Wireb/ICE40LP384_RPi_breakout/iCEcube2/PiDRO_Implmnt/sbt/outputs/placer/PiDRO_sbt.pcf

set_location SPI.SDO_RNO 5 3 6 # SB_LUT4 (LogicCell: SPI.SDO_LC_0)
set_location SPI.SDO 5 3 6 # SB_DFFNE (LogicCell: SPI.SDO_LC_0)
set_location SPI.SDO_RNO_0 5 4 7 # SB_LUT4 (LogicCell: SPI.SDO_RNO_0_LC_1)
set_location SPI.shift_reg_RNO[1] 2 2 5 # SB_LUT4 (LogicCell: SPI.shift_reg[1]_LC_2)
set_location SPI.shift_reg[1] 2 2 5 # SB_DFFN (LogicCell: SPI.shift_reg[1]_LC_2)
set_location SPI.shift_reg_RNO[10] 2 3 0 # SB_LUT4 (LogicCell: SPI.shift_reg[10]_LC_3)
set_location SPI.shift_reg[10] 2 3 0 # SB_DFFN (LogicCell: SPI.shift_reg[10]_LC_3)
set_location SPI.shift_reg_RNO[100] 4 1 1 # SB_LUT4 (LogicCell: SPI.shift_reg[100]_LC_4)
set_location SPI.shift_reg[100] 4 1 1 # SB_DFFN (LogicCell: SPI.shift_reg[100]_LC_4)
set_location SPI.shift_reg_RNO[101] 4 1 6 # SB_LUT4 (LogicCell: SPI.shift_reg[101]_LC_5)
set_location SPI.shift_reg[101] 4 1 6 # SB_DFFN (LogicCell: SPI.shift_reg[101]_LC_5)
set_location SPI.shift_reg_RNO[102] 4 1 3 # SB_LUT4 (LogicCell: SPI.shift_reg[102]_LC_6)
set_location SPI.shift_reg[102] 4 1 3 # SB_DFFN (LogicCell: SPI.shift_reg[102]_LC_6)
set_location SPI.shift_reg_RNO[103] 4 1 4 # SB_LUT4 (LogicCell: SPI.shift_reg[103]_LC_7)
set_location SPI.shift_reg[103] 4 1 4 # SB_DFFN (LogicCell: SPI.shift_reg[103]_LC_7)
set_location SPI.shift_reg_RNO[104] 4 1 2 # SB_LUT4 (LogicCell: SPI.shift_reg[104]_LC_8)
set_location SPI.shift_reg[104] 4 1 2 # SB_DFFN (LogicCell: SPI.shift_reg[104]_LC_8)
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
set_location SPI.shift_reg[97] 5 1 3 # SB_DFFN (LogicCell: SPI.shift_reg[97]_LC_118)
set_location SPI.shift_reg_RNO[98] 5 1 2 # SB_LUT4 (LogicCell: SPI.shift_reg[98]_LC_119)
set_location SPI.shift_reg[98] 5 1 2 # SB_DFFN (LogicCell: SPI.shift_reg[98]_LC_119)
set_location SPI.shift_reg_RNO[99] 5 1 0 # SB_LUT4 (LogicCell: SPI.shift_reg[99]_LC_120)
set_location SPI.shift_reg[99] 5 1 0 # SB_DFFN (LogicCell: SPI.shift_reg[99]_LC_120)
set_location SPI.shift_reg_0_THRU_LUT4_0 2 1 7 # SB_LUT4 (LogicCell: SPI.shift_reg[0]_LC_121)
set_location SPI.shift_reg[0] 2 1 7 # SB_DFFN (LogicCell: SPI.shift_reg[0]_LC_121)
set_location SPI.shift_reg_rst_THRU_LUT4_0 3 3 0 # SB_LUT4 (LogicCell: SPI.shift_reg_rst_LC_122)
set_location SPI.shift_reg_rst 3 3 0 # SB_DFFNR (LogicCell: SPI.shift_reg_rst_LC_122)
set_location SPI.shift_reg_rst_fast_THRU_LUT4_0 5 2 6 # SB_LUT4 (LogicCell: SPI.shift_reg_rst_fast_LC_123)
set_location SPI.shift_reg_rst_fast 5 2 6 # SB_DFFNR (LogicCell: SPI.shift_reg_rst_fast_LC_123)
set_location SPI.shift_reg_rst_fast_0_THRU_LUT4_0 3 3 2 # SB_LUT4 (LogicCell: SPI.shift_reg_rst_fast_0_LC_124)
set_location SPI.shift_reg_rst_fast_0 3 3 2 # SB_DFFNR (LogicCell: SPI.shift_reg_rst_fast_0_LC_124)
set_location SPI.shift_reg_rst_fast_fast_THRU_LUT4_0 3 3 3 # SB_LUT4 (LogicCell: SPI.shift_reg_rst_fast_fast_LC_125)
set_location SPI.shift_reg_rst_fast_fast 3 3 3 # SB_DFFNR (LogicCell: SPI.shift_reg_rst_fast_fast_LC_125)
set_location SPI.shift_reg_rst_fast_rep1_THRU_LUT4_0 3 1 4 # SB_LUT4 (LogicCell: SPI.shift_reg_rst_fast_rep1_LC_126)
set_location SPI.shift_reg_rst_fast_rep1 3 1 4 # SB_DFFNR (LogicCell: SPI.shift_reg_rst_fast_rep1_LC_126)
set_location SPI.shift_reg_rst_rep1_THRU_LUT4_0 3 3 5 # SB_LUT4 (LogicCell: SPI.shift_reg_rst_rep1_LC_127)
set_location SPI.shift_reg_rst_rep1 3 3 5 # SB_DFFNR (LogicCell: SPI.shift_reg_rst_rep1_LC_127)
set_location SPI.shift_reg_rst_rep1_0_THRU_LUT4_0 3 3 6 # SB_LUT4 (LogicCell: SPI.shift_reg_rst_rep1_0_LC_128)
set_location SPI.shift_reg_rst_rep1_0 3 3 6 # SB_DFFNR (LogicCell: SPI.shift_reg_rst_rep1_0_LC_128)
set_location SPI.shift_reg_rst_rep1_fast_THRU_LUT4_0 3 3 7 # SB_LUT4 (LogicCell: SPI.shift_reg_rst_rep1_fast_LC_129)
set_location SPI.shift_reg_rst_rep1_fast 3 3 7 # SB_DFFNR (LogicCell: SPI.shift_reg_rst_rep1_fast_LC_129)
set_location SPI.shift_reg_rst_rep1_rep1_THRU_LUT4_0 4 6 0 # SB_LUT4 (LogicCell: SPI.shift_reg_rst_rep1_rep1_LC_130)
set_location SPI.shift_reg_rst_rep1_rep1 4 6 0 # SB_DFFNR (LogicCell: SPI.shift_reg_rst_rep1_rep1_LC_130)
set_location SPI.shift_reg_rst_rep2_THRU_LUT4_0 4 6 1 # SB_LUT4 (LogicCell: SPI.shift_reg_rst_rep2_LC_131)
set_location SPI.shift_reg_rst_rep2 4 6 1 # SB_DFFNR (LogicCell: SPI.shift_reg_rst_rep2_LC_131)
set_location SPI.shift_reg_rst_rep2_fast_THRU_LUT4_0 4 6 2 # SB_LUT4 (LogicCell: SPI.shift_reg_rst_rep2_fast_LC_132)
set_location SPI.shift_reg_rst_rep2_fast 4 6 2 # SB_DFFNR (LogicCell: SPI.shift_reg_rst_rep2_fast_LC_132)
set_location SPI.shift_reg_rst_rep2_rep1_THRU_LUT4_0 4 6 3 # SB_LUT4 (LogicCell: SPI.shift_reg_rst_rep2_rep1_LC_133)
set_location SPI.shift_reg_rst_rep2_rep1 4 6 3 # SB_DFFNR (LogicCell: SPI.shift_reg_rst_rep2_rep1_LC_133)
set_location GND -1 -1 -1 # GND
set_io LED_obuf 7 4 0 # ICE_IO
set_io SPI_SDI_ibuf 5 0 1 # ICE_IO
set_io SPI_SDO_obuf 5 0 0 # ICE_IO
set_io SPI_SS_ibuf 6 0 1 # ICE_IO
set_io SPI_SCK_ibuf_gb_io 6 0 0 # ICE_IO
set_io SPI_SCK_ibuf_gb_io_gb 0 5 0 # ICE_GB
set_location INV_SPI_SCK_c_g -1 -1 -1 # INV
set_location CONSTANT_ONE_LUT4 5 6 7 # SB_LUT4 (LogicCell: LC_134)
