Wireb/ICE40LP384_RPi_breakout/iCEcube2/PiDRO_Implmnt/sbt/outputs/simulation_netlist/main_sbt.vhd

-- ******************************************************************************

-- iCEcube Netlister

-- Version:            2020.12.27943

-- Build Date:         Dec  9 2020 18:18:06

-- File Generated:     Mar 20 2022 17:01:08

-- Purpose:            Post-Route Verilog/VHDL netlist for timing simulation

-- Copyright (C) 2006-2010 by Lattice Semiconductor Corp. All rights reserved.

-- ******************************************************************************

-- VHDL file for cell "main" view "INTERFACE"

library ieee;
use ieee.std_logic_1164.all;
use ieee.std_logic_arith.all;
use ieee.std_logic_unsigned.all;

library ice;
use ice.vcomponent_vital.all;

-- Entity of main
entity main is
port (
    SPI_SS : in std_logic;
    SPI_SDO : out std_logic;
    SPI_SDI : in std_logic;
    LED : out std_logic;
    SPI_SCK : in std_logic);
end main;

-- Architecture of main
-- View name is \INTERFACE\
architecture \INTERFACE\ of main is

signal \N__724\ : std_logic;
signal \N__723\ : std_logic;
signal \N__722\ : std_logic;
signal \N__715\ : std_logic;
signal \N__714\ : std_logic;
signal \N__713\ : std_logic;
signal \N__706\ : std_logic;
signal \N__705\ : std_logic;
signal \N__704\ : std_logic;
signal \N__697\ : std_logic;
signal \N__696\ : std_logic;
signal \N__695\ : std_logic;
signal \N__688\ : std_logic;
signal \N__687\ : std_logic;
signal \N__686\ : std_logic;
signal \N__669\ : std_logic;
signal \N__666\ : std_logic;
signal \N__663\ : std_logic;
signal \N__660\ : std_logic;
signal \N__657\ : std_logic;
signal \N__654\ : std_logic;
signal \N__651\ : std_logic;
signal \N__648\ : std_logic;
signal \N__645\ : std_logic;
signal \N__642\ : std_logic;
signal \N__639\ : std_logic;
signal \N__636\ : std_logic;
signal \N__633\ : std_logic;
signal \N__630\ : std_logic;
signal \N__627\ : std_logic;
signal \N__624\ : std_logic;
signal \N__621\ : std_logic;
signal \N__618\ : std_logic;
signal \N__615\ : std_logic;
signal \N__612\ : std_logic;
signal \N__609\ : std_logic;
signal \N__606\ : std_logic;
signal \N__603\ : std_logic;
signal \N__600\ : std_logic;
signal \N__597\ : std_logic;
signal \N__594\ : std_logic;
signal \N__591\ : std_logic;
signal \N__590\ : std_logic;
signal \N__587\ : std_logic;
signal \N__584\ : std_logic;
signal \N__581\ : std_logic;
signal \N__580\ : std_logic;
signal \N__577\ : std_logic;
signal \N__576\ : std_logic;
signal \N__575\ : std_logic;
signal \N__564\ : std_logic;
signal \N__561\ : std_logic;
signal \N__558\ : std_logic;
signal \N__555\ : std_logic;
signal \N__552\ : std_logic;
signal \N__549\ : std_logic;
signal \N__546\ : std_logic;
signal \N__543\ : std_logic;
signal \N__540\ : std_logic;
signal \N__537\ : std_logic;
signal \N__534\ : std_logic;
signal \N__531\ : std_logic;
signal \N__528\ : std_logic;
signal \N__525\ : std_logic;
signal \N__522\ : std_logic;
signal \N__519\ : std_logic;
signal \N__516\ : std_logic;
signal \N__513\ : std_logic;
signal \N__510\ : std_logic;
signal \N__507\ : std_logic;
signal \N__504\ : std_logic;
signal \N__501\ : std_logic;
signal \N__498\ : std_logic;
signal \N__495\ : std_logic;
signal \N__492\ : std_logic;
signal \N__489\ : std_logic;
signal \N__486\ : std_logic;
signal \N__483\ : std_logic;
signal \N__480\ : std_logic;
signal \N__477\ : std_logic;
signal \N__474\ : std_logic;
signal \N__471\ : std_logic;
signal \N__468\ : std_logic;
signal \N__465\ : std_logic;
signal \N__462\ : std_logic;
signal \N__459\ : std_logic;
signal \N__456\ : std_logic;
signal \N__453\ : std_logic;
signal \N__450\ : std_logic;
signal \N__447\ : std_logic;
signal \N__444\ : std_logic;
signal \N__441\ : std_logic;
signal \N__438\ : std_logic;
signal \N__435\ : std_logic;
signal \N__434\ : std_logic;
signal \N__433\ : std_logic;
signal \N__432\ : std_logic;
signal \N__423\ : std_logic;
signal \N__420\ : std_logic;
signal \N__417\ : std_logic;
signal \N__414\ : std_logic;
signal \N__411\ : std_logic;
signal \N__408\ : std_logic;
signal \SPI_SS_ibuf_gb_io_gb_input\ : std_logic;
signal \SPI_SCK_c_g\ : std_logic;
signal \SPI_SCK_ibuf_gb_io_gb_input\ : std_logic;
signal \GNDG0\ : std_logic;
signal \VCCG0\ : std_logic;
signal \SPI.shift_regZ0Z_15\ : std_logic;
signal \SPI.shift_regZ0Z_16\ : std_logic;
signal \SPI.shift_regZ0Z_14\ : std_logic;
signal \SPI.shift_regZ0Z_17\ : std_logic;
signal \SPI.shift_regZ0Z_11\ : std_logic;
signal \SPI.shift_regZ0Z_12\ : std_logic;
signal \SPI.shift_regZ0Z_13\ : std_logic;
signal \INVSPI.shift_reg_15C_net\ : std_logic;
signal \SPI_SDI_c\ : std_logic;
signal \SPI.shift_regZ0Z_0\ : std_logic;
signal \SPI.shift_regZ0Z_1\ : std_logic;
signal \SPI.shift_regZ0Z_18\ : std_logic;
signal \SPI.shift_regZ0Z_19\ : std_logic;
signal \SPI.shift_regZ0Z_20\ : std_logic;
signal \SPI.shift_regZ0Z_21\ : std_logic;
signal \SPI.shift_regZ0Z_22\ : std_logic;
signal \INVSPI.shift_reg_22C_net\ : std_logic;
signal \SPI.shift_regZ0Z_10\ : std_logic;
signal \SPI.shift_regZ0Z_2\ : std_logic;
signal \SPI.shift_regZ0Z_3\ : std_logic;
signal \SPI.shift_regZ0Z_7\ : std_logic;
signal \SPI.shift_regZ0Z_8\ : std_logic;
signal \SPI.shift_regZ0Z_9\ : std_logic;
signal \SPI.shift_regZ0Z_4\ : std_logic;
signal \SPI.shift_regZ0Z_5\ : std_logic;
signal \SPI.shift_regZ0Z_6\ : std_logic;
signal \INVSPI.shift_reg_7C_net\ : std_logic;
signal \SPI.shift_regZ0Z_23\ : std_logic;
signal \SPI_SDO_c\ : std_logic;
signal \INVSPI.SDOC_net\ : std_logic;
signal \SPI.LED_c_i\ : std_logic;
signal \LED_c_g\ : std_logic;
signal \GB_BUFFER_LED_c_g_THRU_CO\ : std_logic;
signal \_gnd_net_\ : std_logic;

signal \LED_wire\ : std_logic;
signal \SPI_SDO_wire\ : std_logic;
signal \SPI_SDI_wire\ : std_logic;
signal \SPI_SCK_wire\ : std_logic;
signal \SPI_SS_wire\ : std_logic;

begin
    LED <= \LED_wire\;
    SPI_SDO <= \SPI_SDO_wire\;
    \SPI_SDI_wire\ <= SPI_SDI;
    \SPI_SCK_wire\ <= SPI_SCK;
    \SPI_SS_wire\ <= SPI_SS;

    \LED_obuf_iopad\ : IO_PAD
    generic map (
            IO_STANDARD => "SB_LVCMOS",
            PULLUP => '0'
        )
    port map (
            OE => \N__724\,
            DIN => \N__723\,
            DOUT => \N__722\,
            PACKAGEPIN => \LED_wire\
        );

    \LED_obuf_preio\ : PRE_IO
    generic map (
            NEG_TRIGGER => '0',
            PIN_TYPE => "011001"
        )
    port map (
            PADOEN => \N__724\,
            PADOUT => \N__723\,
            PADIN => \N__722\,
            CLOCKENABLE => 'H',
            DOUT1 => '0',
            OUTPUTENABLE => '0',
            DIN0 => OPEN,
            DOUT0 => \N__558\,
            INPUTCLK => '0',
            LATCHINPUTVALUE => '0',
            DIN1 => OPEN,
            OUTPUTCLK => '0'
        );

    \SPI_SDO_obuf_iopad\ : IO_PAD
    generic map (
            IO_STANDARD => "SB_LVCMOS",
            PULLUP => '0'
        )
    port map (
            OE => \N__715\,
            DIN => \N__714\,
            DOUT => \N__713\,
            PACKAGEPIN => \SPI_SDO_wire\
        );

    \SPI_SDO_obuf_preio\ : PRE_IO
    generic map (
            NEG_TRIGGER => '0',
            PIN_TYPE => "011001"
        )
    port map (
            PADOEN => \N__715\,
            PADOUT => \N__714\,
            PADIN => \N__713\,
            CLOCKENABLE => 'H',
            DOUT1 => '0',
            OUTPUTENABLE => '0',
            DIN0 => OPEN,
            DOUT0 => \N__615\,
            INPUTCLK => '0',
            LATCHINPUTVALUE => '0',
            DIN1 => OPEN,
            OUTPUTCLK => '0'
        );

    \SPI_SDI_ibuf_iopad\ : IO_PAD
    generic map (
            IO_STANDARD => "SB_LVCMOS",
            PULLUP => '0'
        )
    port map (
            OE => \N__706\,
            DIN => \N__705\,
            DOUT => \N__704\,
            PACKAGEPIN => \SPI_SDI_wire\
        );

    \SPI_SDI_ibuf_preio\ : PRE_IO
    generic map (
            NEG_TRIGGER => '0',
            PIN_TYPE => "000001"
        )
    port map (
            PADOEN => \N__706\,
            PADOUT => \N__705\,
            PADIN => \N__704\,
            CLOCKENABLE => 'H',
            DOUT1 => '0',
            OUTPUTENABLE => '0',
            DIN0 => \SPI_SDI_c\,
            DOUT0 => '0',
            INPUTCLK => '0',
            LATCHINPUTVALUE => '0',
            DIN1 => OPEN,
            OUTPUTCLK => '0'
        );

    \SPI_SCK_ibuf_gb_io_iopad\ : IO_PAD
    generic map (
            IO_STANDARD => "SB_LVCMOS",
            PULLUP => '0'
        )
    port map (
            OE => \N__697\,
            DIN => \N__696\,
            DOUT => \N__695\,
            PACKAGEPIN => \SPI_SCK_wire\
        );

    \SPI_SCK_ibuf_gb_io_preio\ : PRE_IO
    generic map (
            NEG_TRIGGER => '0',
            PIN_TYPE => "000001"
        )
    port map (
            PADOEN => \N__697\,
            PADOUT => \N__696\,
            PADIN => \N__695\,
            CLOCKENABLE => 'H',
            DOUT1 => '0',
            OUTPUTENABLE => '0',
            DIN0 => \SPI_SCK_ibuf_gb_io_gb_input\,
            DOUT0 => '0',
            INPUTCLK => '0',
            LATCHINPUTVALUE => '0',
            DIN1 => OPEN,
            OUTPUTCLK => '0'
        );

    \SPI_SS_ibuf_gb_io_iopad\ : IO_PAD
    generic map (
            IO_STANDARD => "SB_LVCMOS",
            PULLUP => '0'
        )
    port map (
            OE => \N__688\,
            DIN => \N__687\,
            DOUT => \N__686\,
            PACKAGEPIN => \SPI_SS_wire\
        );

    \SPI_SS_ibuf_gb_io_preio\ : PRE_IO
    generic map (
            NEG_TRIGGER => '0',
            PIN_TYPE => "000001"
        )
    port map (
            PADOEN => \N__688\,
            PADOUT => \N__687\,
            PADIN => \N__686\,
            CLOCKENABLE => 'H',
            DOUT1 => '0',
            OUTPUTENABLE => '0',
            DIN0 => \SPI_SS_ibuf_gb_io_gb_input\,
            DOUT0 => '0',
            INPUTCLK => '0',
            LATCHINPUTVALUE => '0',
            DIN1 => OPEN,
            OUTPUTCLK => '0'
        );

    \I__128\ : InMux
    port map (
            O => \N__669\,
            I => \N__666\
        );

    \I__127\ : LocalMux
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
            in2 => \_gnd_net_\,
            in3 => \N__621\,
            lcout => \SPI_SDO_c\,
            ltout => OPEN,
            carryin => \_gnd_net_\,
            carryout => OPEN,
            clk => \INVSPI.SDOC_net\,
            ce => \N__603\,
            sr => \_gnd_net_\
        );

    \SPI.SDO_RNO_LC_3_2_5\ : LogicCell40
    generic map (
            C_ON => '0',
            SEQ_MODE => "0000",
            LUT_INIT => "0000000011111111"
        )
    port map (
            in0 => \_gnd_net_\,
            in1 => \_gnd_net_\,
            in2 => \_gnd_net_\,
            in3 => \N__590\,
            lcout => \SPI.LED_c_i\,
            ltout => OPEN,
            carryin => \_gnd_net_\,
            carryout => OPEN,
            clk => \_gnd_net_\,
            ce => 'H',
            sr => \_gnd_net_\
        );

    \GB_BUFFER_LED_c_g_THRU_LUT4_0_LC_6_4_1\ : LogicCell40
    generic map (
            C_ON => '0',
            SEQ_MODE => "0000",
            LUT_INIT => "1010101010101010"
        )
    port map (
            in0 => \N__591\,
            in1 => \_gnd_net_\,
            in2 => \_gnd_net_\,
            in3 => \_gnd_net_\,
            lcout => \GB_BUFFER_LED_c_g_THRU_CO\,
            ltout => OPEN,
            carryin => \_gnd_net_\,
            carryout => OPEN,
            clk => \_gnd_net_\,
            ce => 'H',
            sr => \_gnd_net_\
        );
end \INTERFACE\;
