Wireb/ICE40LP384_RPi_breakout/iCEcube2/PiDRO_Implmnt/sbt/outputs/simulation_netlist/PiDRO_sbt.v

// ******************************************************************************

// iCEcube Netlister

// Version:            2020.12.27943

// Build Date:         Dec  9 2020 18:18:12

// File Generated:     May 3 2022 18:25:36

// Purpose:            Post-Route Verilog/VHDL netlist for timing simulation

// Copyright (C) 2006-2010 by Lattice Semiconductor Corp. All rights reserved.

// ******************************************************************************

// Verilog file for cell "PiDRO" view "INTERFACE"

module PiDRO (
    Y_R,
    Y_B,
    B_R,
    B_B,
    Z_A,
    Y_A,
    X_R,
    X_B,
    SPI_SDI,
    Z_R,
    Z_B,
    SPI_SCK,
    A_R,
    A_B,
    SPI_SS,
    SPI_SDO,
    LED,
    B_A,
    A_A,
    X_A);

    input Y_R;
    input Y_B;
    input B_R;
    input B_B;
    input Z_A;
    input Y_A;
    input X_R;
    input X_B;
    input SPI_SDI;
    input Z_R;
    input Z_B;
    input SPI_SCK;
    input A_R;
    input A_B;
    input SPI_SS;
    output SPI_SDO;
    output LED;
    input B_A;
    input A_A;
    input X_A;

    wire N__3253;
    wire N__3252;
    wire N__3251;
    wire N__3244;
    wire N__3243;
    wire N__3242;
    wire N__3235;
    wire N__3234;
    wire N__3233;
    wire N__3226;
    wire N__3225;
    wire N__3224;
    wire N__3217;
    wire N__3216;
    wire N__3215;
    wire N__3198;
    wire N__3195;
    wire N__3192;
    wire N__3189;
    wire N__3186;
    wire N__3183;
    wire N__3180;
    wire N__3177;
    wire N__3174;
    wire N__3171;
    wire N__3168;
    wire N__3165;
    wire N__3162;
    wire N__3161;
    wire N__3160;
    wire N__3159;
    wire N__3158;
    wire N__3157;
    wire N__3156;
    wire N__3155;
    wire N__3154;
    wire N__3153;
    wire N__3138;
    wire N__3131;
    wire N__3126;
    wire N__3123;
    wire N__3120;
    wire N__3117;
    wire N__3114;
    wire N__3111;
    wire N__3110;
    wire N__3109;
    wire N__3108;
    wire N__3107;
    wire N__3106;
    wire N__3105;
    wire N__3102;
    wire N__3089;
    wire N__3088;
    wire N__3083;
    wire N__3080;
    wire N__3079;
    wire N__3078;
    wire N__3077;
    wire N__3076;
    wire N__3073;
    wire N__3070;
    wire N__3061;
    wire N__3054;
    wire N__3051;
    wire N__3048;
    wire N__3045;
    wire N__3042;
    wire N__3039;
    wire N__3036;
    wire N__3033;
    wire N__3030;
    wire N__3027;
    wire N__3024;
    wire N__3023;
    wire N__3022;
    wire N__3021;
    wire N__3020;
    wire N__3019;
    wire N__3018;
    wire N__3017;
    wire N__3016;
    wire N__3015;
    wire N__3010;
    wire N__2997;
    wire N__2992;
    wire N__2985;
    wire N__2984;
    wire N__2983;
    wire N__2982;
    wire N__2981;
    wire N__2980;
    wire N__2979;
    wire N__2978;
    wire N__2977;
    wire N__2976;
    wire N__2973;
    wire N__2970;
    wire N__2965;
    wire N__2952;
    wire N__2949;
    wire N__2940;
    wire N__2937;
    wire N__2934;
    wire N__2931;
    wire N__2928;
    wire N__2925;
    wire N__2924;
    wire N__2923;
    wire N__2920;
    wire N__2919;
    wire N__2916;
    wire N__2915;
    wire N__2914;
    wire N__2911;
    wire N__2908;
    wire N__2905;
    wire N__2902;
    wire N__2899;
    wire N__2896;
    wire N__2893;
    wire N__2890;
    wire N__2887;
    wire N__2882;
    wire N__2879;
    wire N__2876;
    wire N__2871;
    wire N__2862;
    wire N__2859;
    wire N__2856;
    wire N__2853;
    wire N__2850;
    wire N__2847;
    wire N__2844;
    wire N__2841;
    wire N__2838;
    wire N__2835;
    wire N__2832;
    wire N__2829;
    wire N__2826;
    wire N__2823;
    wire N__2820;
    wire N__2817;
    wire N__2814;
    wire N__2811;
    wire N__2810;
    wire N__2809;
    wire N__2808;
    wire N__2807;
    wire N__2806;
    wire N__2805;
    wire N__2804;
    wire N__2803;
    wire N__2802;
    wire N__2797;
    wire N__2780;
    wire N__2775;
    wire N__2772;
    wire N__2769;
    wire N__2766;
    wire N__2763;
    wire N__2760;
    wire N__2757;
    wire N__2754;
    wire N__2751;
    wire N__2748;
    wire N__2745;
    wire N__2742;
    wire N__2739;
    wire N__2738;
    wire N__2737;
    wire N__2736;
    wire N__2735;
    wire N__2734;
    wire N__2733;
    wire N__2732;
    wire N__2731;
    wire N__2730;
    wire N__2721;
    wire N__2718;
    wire N__2715;
    wire N__2706;
    wire N__2703;
    wire N__2694;
    wire N__2691;
    wire N__2688;
    wire N__2685;
    wire N__2682;
    wire N__2679;
    wire N__2676;
    wire N__2675;
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
    wire \SPI.N_481_fast_fast ;
    wire \SPI.shift_regZ0Z_119 ;
    wire SPI_SDO_c;
    wire \INVSPI.SDOC_net ;
    wire LED_c;
    wire \SPI.LED_c_i ;
    wire \SPI.shift_regZ0Z_72 ;
    wire \SPI.shift_regZ0Z_73 ;
    wire \SPI.shift_regZ0Z_74 ;
    wire \SPI.shift_regZ0Z_77 ;
    wire \SPI.shift_regZ0Z_75 ;
    wire \SPI.shift_regZ0Z_76 ;
    wire \SPI.N_481_rep1_rep1 ;
    wire \SPI.shift_regZ0Z_78 ;
    wire \SPI.shift_regZ0Z_79 ;
    wire \INVSPI.shift_reg_78C_net ;
    wire CONSTANT_ONE_NET;
    wire _gnd_net_;

    IO_PAD LED_obuf_iopad (
            .OE(N__3253),
            .DIN(N__3252),
            .DOUT(N__3251),
            .PACKAGEPIN(LED));
    defparam LED_obuf_preio.NEG_TRIGGER=1'b0;
    defparam LED_obuf_preio.PIN_TYPE=6'b011001;
    PRE_IO LED_obuf_preio (
            .PADOEN(N__3253),
            .PADOUT(N__3252),
            .PADIN(N__3251),
            .CLOCKENABLE(),
            .DOUT1(),
            .OUTPUTENABLE(),
            .DIN0(),
            .DOUT0(N__2915),
            .INPUTCLK(),
            .LATCHINPUTVALUE(),
            .DIN1(),
            .OUTPUTCLK());
    IO_PAD SPI_SS_ibuf_iopad (
            .OE(N__3244),
            .DIN(N__3243),
            .DOUT(N__3242),
            .PACKAGEPIN(SPI_SS));
    defparam SPI_SS_ibuf_preio.NEG_TRIGGER=1'b0;
    defparam SPI_SS_ibuf_preio.PIN_TYPE=6'b000001;
    PRE_IO SPI_SS_ibuf_preio (
            .PADOEN(N__3244),
            .PADOUT(N__3243),
            .PADIN(N__3242),
            .CLOCKENABLE(),
            .DOUT1(),
            .OUTPUTENABLE(),
            .DIN0(LED_c),
            .DOUT0(),
            .INPUTCLK(),
            .LATCHINPUTVALUE(),
            .DIN1(),
            .OUTPUTCLK());
    IO_PAD SPI_SDO_obuf_iopad (
            .OE(N__3235),
            .DIN(N__3234),
            .DOUT(N__3233),
            .PACKAGEPIN(SPI_SDO));
    defparam SPI_SDO_obuf_preio.NEG_TRIGGER=1'b0;
    defparam SPI_SDO_obuf_preio.PIN_TYPE=6'b011001;
    PRE_IO SPI_SDO_obuf_preio (
            .PADOEN(N__3235),
            .PADOUT(N__3234),
            .PADIN(N__3233),
            .CLOCKENABLE(),
            .DOUT1(),
            .OUTPUTENABLE(),
            .DIN0(),
            .DOUT0(N__2934),
            .INPUTCLK(),
            .LATCHINPUTVALUE(),
            .DIN1(),
            .OUTPUTCLK());
    IO_PAD SPI_SDI_ibuf_iopad (
            .OE(N__3226),
            .DIN(N__3225),
            .DOUT(N__3224),
            .PACKAGEPIN(SPI_SDI));
    defparam SPI_SDI_ibuf_preio.NEG_TRIGGER=1'b0;
    defparam SPI_SDI_ibuf_preio.PIN_TYPE=6'b000001;
    PRE_IO SPI_SDI_ibuf_preio (
            .PADOEN(N__3226),
            .PADOUT(N__3225),
            .PADIN(N__3224),
            .CLOCKENABLE(),
            .DOUT1(),
            .OUTPUTENABLE(),
            .DIN0(SPI_SDI_c),
            .DOUT0(),
            .INPUTCLK(),
            .LATCHINPUTVALUE(),
            .DIN1(),
            .OUTPUTCLK());
    IO_PAD SPI_SCK_ibuf_gb_io_iopad (
            .OE(N__3217),
            .DIN(N__3216),
            .DOUT(N__3215),
            .PACKAGEPIN(SPI_SCK));
    defparam SPI_SCK_ibuf_gb_io_preio.NEG_TRIGGER=1'b0;
    defparam SPI_SCK_ibuf_gb_io_preio.PIN_TYPE=6'b000001;
    PRE_IO SPI_SCK_ibuf_gb_io_preio (
            .PADOEN(N__3217),
            .PADOUT(N__3216),
            .PADIN(N__3215),
            .CLOCKENABLE(),
            .DOUT1(),
            .OUTPUTENABLE(),
            .DIN0(SPI_SCK_ibuf_gb_io_gb_input),
            .DOUT0(),
            .INPUTCLK(),
            .LATCHINPUTVALUE(),
            .DIN1(),
            .OUTPUTCLK());
    InMux I__642 (
            .O(N__3198),
            .I(N__3195));
    LocalMux I__641 (
            .O(N__3195),
            .I(\SPI.shift_regZ0Z_72 ));
    InMux I__640 (
            .O(N__3192),
            .I(N__3189));
    LocalMux I__639 (
            .O(N__3189),
            .I(\SPI.shift_regZ0Z_73 ));
    InMux I__638 (
            .O(N__3186),
            .I(N__3183));
    LocalMux I__637 (
            .O(N__3183),
            .I(\SPI.shift_regZ0Z_74 ));
    InMux I__636 (
            .O(N__3180),
            .I(N__3177));
    LocalMux I__635 (
            .O(N__3177),
            .I(\SPI.shift_regZ0Z_77 ));
    InMux I__634 (
            .O(N__3174),
            .I(N__3171));
    LocalMux I__633 (
            .O(N__3171),
            .I(\SPI.shift_regZ0Z_75 ));
    InMux I__632 (
            .O(N__3168),
            .I(N__3165));
    LocalMux I__631 (
            .O(N__3165),
            .I(\SPI.shift_regZ0Z_76 ));
    InMux I__630 (
            .O(N__3162),
            .I(N__3138));
    InMux I__629 (
            .O(N__3161),
            .I(N__3138));
    InMux I__628 (
            .O(N__3160),
            .I(N__3138));
    InMux I__627 (
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
            .sr(_gnd_net_));
    defparam \SPI.shift_reg_113_LC_3_2_4 .C_ON=1'b0;
    defparam \SPI.shift_reg_113_LC_3_2_4 .SEQ_MODE=4'b1000;
    defparam \SPI.shift_reg_113_LC_3_2_4 .LUT_INIT=16'b1010101000000000;
    LogicCell40 \SPI.shift_reg_113_LC_3_2_4  (
            .in0(N__2980),
            .in1(_gnd_net_),
            .in2(_gnd_net_),
            .in3(N__1983),
            .lcout(\SPI.shift_regZ0Z_113 ),
            .ltout(),
            .carryin(_gnd_net_),
            .carryout(),
            .clk(\INVSPI.shift_reg_109C_net ),
            .ce(),
            .sr(_gnd_net_));
    defparam \SPI.shift_reg_114_LC_3_2_5 .C_ON=1'b0;
    defparam \SPI.shift_reg_114_LC_3_2_5 .SEQ_MODE=4'b1000;
    defparam \SPI.shift_reg_114_LC_3_2_5 .LUT_INIT=16'b1100110000000000;
    LogicCell40 \SPI.shift_reg_114_LC_3_2_5  (
            .in0(_gnd_net_),
            .in1(N__2977),
            .in2(_gnd_net_),
            .in3(N__1977),
            .lcout(\SPI.shift_regZ0Z_114 ),
            .ltout(),
            .carryin(_gnd_net_),
            .carryout(),
            .clk(\INVSPI.shift_reg_109C_net ),
            .ce(),
            .sr(_gnd_net_));
    defparam \SPI.shift_reg_115_LC_3_2_6 .C_ON=1'b0;
    defparam \SPI.shift_reg_115_LC_3_2_6 .SEQ_MODE=4'b1000;
    defparam \SPI.shift_reg_115_LC_3_2_6 .LUT_INIT=16'b1010101000000000;
    LogicCell40 \SPI.shift_reg_115_LC_3_2_6  (
            .in0(N__2981),
            .in1(_gnd_net_),
            .in2(_gnd_net_),
            .in3(N__1971),
            .lcout(\SPI.shift_regZ0Z_115 ),
            .ltout(),
            .carryin(_gnd_net_),
            .carryout(),
            .clk(\INVSPI.shift_reg_109C_net ),
            .ce(),
            .sr(_gnd_net_));
    defparam \SPI.shift_reg_116_LC_3_2_7 .C_ON=1'b0;
    defparam \SPI.shift_reg_116_LC_3_2_7 .SEQ_MODE=4'b1000;
    defparam \SPI.shift_reg_116_LC_3_2_7 .LUT_INIT=16'b1100110000000000;
    LogicCell40 \SPI.shift_reg_116_LC_3_2_7  (
            .in0(_gnd_net_),
            .in1(N__2978),
            .in2(_gnd_net_),
            .in3(N__2061),
            .lcout(\SPI.shift_regZ0Z_116 ),
            .ltout(),
            .carryin(_gnd_net_),
            .carryout(),
            .clk(\INVSPI.shift_reg_109C_net ),
            .ce(),
            .sr(_gnd_net_));
    defparam \SPI.shift_reg_rst_LC_3_3_0 .C_ON=1'b0;
    defparam \SPI.shift_reg_rst_LC_3_3_0 .SEQ_MODE=4'b1010;
    defparam \SPI.shift_reg_rst_LC_3_3_0 .LUT_INIT=16'b1010101010101010;
    LogicCell40 \SPI.shift_reg_rst_LC_3_3_0  (
            .in0(N__3105),
            .in1(_gnd_net_),
            .in2(_gnd_net_),
            .in3(_gnd_net_),
            .lcout(\SPI.shift_reg_rstZ0 ),
            .ltout(),
            .carryin(_gnd_net_),
            .carryout(),
            .clk(\INVSPI.shift_reg_rstC_net ),
            .ce(),
            .sr(N__2924));
    defparam \SPI.shift_reg_rst_fast_0_LC_3_3_2 .C_ON=1'b0;
    defparam \SPI.shift_reg_rst_fast_0_LC_3_3_2 .SEQ_MODE=4'b1010;
    defparam \SPI.shift_reg_rst_fast_0_LC_3_3_2 .LUT_INIT=16'b1010101010101010;
    LogicCell40 \SPI.shift_reg_rst_fast_0_LC_3_3_2  (
            .in0(N__3106),
            .in1(_gnd_net_),
            .in2(_gnd_net_),
            .in3(_gnd_net_),
            .lcout(\SPI.N_481_fast_0 ),
            .ltout(),
            .carryin(_gnd_net_),
            .carryout(),
            .clk(\INVSPI.shift_reg_rstC_net ),
            .ce(),
            .sr(N__2924));
    defparam \SPI.shift_reg_rst_fast_fast_LC_3_3_3 .C_ON=1'b0;
    defparam \SPI.shift_reg_rst_fast_fast_LC_3_3_3 .SEQ_MODE=4'b1010;
    defparam \SPI.shift_reg_rst_fast_fast_LC_3_3_3 .LUT_INIT=16'b1111111100000000;
    LogicCell40 \SPI.shift_reg_rst_fast_fast_LC_3_3_3  (
            .in0(_gnd_net_),
            .in1(_gnd_net_),
            .in2(_gnd_net_),
            .in3(N__3107),
            .lcout(\SPI.N_481_fast_fast ),
            .ltout(),
            .carryin(_gnd_net_),
            .carryout(),
            .clk(\INVSPI.shift_reg_rstC_net ),
            .ce(),
            .sr(N__2924));
    defparam \SPI.shift_reg_rst_rep1_LC_3_3_5 .C_ON=1'b0;
    defparam \SPI.shift_reg_rst_rep1_LC_3_3_5 .SEQ_MODE=4'b1010;
    defparam \SPI.shift_reg_rst_rep1_LC_3_3_5 .LUT_INIT=16'b1111111100000000;
    LogicCell40 \SPI.shift_reg_rst_rep1_LC_3_3_5  (
            .in0(_gnd_net_),
            .in1(_gnd_net_),
            .in2(_gnd_net_),
            .in3(N__3109),
            .lcout(\SPI.N_481_rep1 ),
            .ltout(),
            .carryin(_gnd_net_),
            .carryout(),
            .clk(\INVSPI.shift_reg_rstC_net ),
            .ce(),
            .sr(N__2924));
    defparam \SPI.shift_reg_rst_rep1_0_LC_3_3_6 .C_ON=1'b0;
    defparam \SPI.shift_reg_rst_rep1_0_LC_3_3_6 .SEQ_MODE=4'b1010;
    defparam \SPI.shift_reg_rst_rep1_0_LC_3_3_6 .LUT_INIT=16'b1010101010101010;
    LogicCell40 \SPI.shift_reg_rst_rep1_0_LC_3_3_6  (
            .in0(N__3108),
            .in1(_gnd_net_),
            .in2(_gnd_net_),
            .in3(_gnd_net_),
            .lcout(\SPI.N_481_rep1_0 ),
            .ltout(),
            .carryin(_gnd_net_),
            .carryout(),
            .clk(\INVSPI.shift_reg_rstC_net ),
            .ce(),
            .sr(N__2924));
    defparam \SPI.shift_reg_rst_rep1_fast_LC_3_3_7 .C_ON=1'b0;
    defparam \SPI.shift_reg_rst_rep1_fast_LC_3_3_7 .SEQ_MODE=4'b1010;
    defparam \SPI.shift_reg_rst_rep1_fast_LC_3_3_7 .LUT_INIT=16'b1111111100000000;
    LogicCell40 \SPI.shift_reg_rst_rep1_fast_LC_3_3_7  (
            .in0(_gnd_net_),
            .in1(_gnd_net_),
            .in2(_gnd_net_),
            .in3(N__3110),
            .lcout(\SPI.N_481_rep1_fast ),
            .ltout(),
            .carryin(_gnd_net_),
            .carryout(),
            .clk(\INVSPI.shift_reg_rstC_net ),
            .ce(),
            .sr(N__2924));
    defparam \SPI.shift_reg_22_LC_3_4_0 .C_ON=1'b0;
    defparam \SPI.shift_reg_22_LC_3_4_0 .SEQ_MODE=4'b1000;
    defparam \SPI.shift_reg_22_LC_3_4_0 .LUT_INIT=16'b1100110000000000;
    LogicCell40 \SPI.shift_reg_22_LC_3_4_0  (
            .in0(_gnd_net_),
            .in1(N__2175),
            .in2(_gnd_net_),
            .in3(N__2079),
            .lcout(\SPI.shift_regZ0Z_22 ),
            .ltout(),
            .carryin(_gnd_net_),
            .carryout(),
            .clk(\INVSPI.shift_reg_22C_net ),
            .ce(),
            .sr(_gnd_net_));
    defparam \SPI.shift_reg_23_LC_3_4_1 .C_ON=1'b0;
    defparam \SPI.shift_reg_23_LC_3_4_1 .SEQ_MODE=4'b1000;
    defparam \SPI.shift_reg_23_LC_3_4_1 .LUT_INIT=16'b1010101000000000;
    LogicCell40 \SPI.shift_reg_23_LC_3_4_1  (
            .in0(N__2180),
            .in1(_gnd_net_),
            .in2(_gnd_net_),
            .in3(N__2019),
            .lcout(\SPI.shift_regZ0Z_23 ),
            .ltout(),
            .carryin(_gnd_net_),
            .carryout(),
            .clk(\INVSPI.shift_reg_22C_net ),
            .ce(),
            .sr(_gnd_net_));
    defparam \SPI.shift_reg_24_LC_3_4_2 .C_ON=1'b0;
    defparam \SPI.shift_reg_24_LC_3_4_2 .SEQ_MODE=4'b1000;
    defparam \SPI.shift_reg_24_LC_3_4_2 .LUT_INIT=16'b1100110000000000;
    LogicCell40 \SPI.shift_reg_24_LC_3_4_2  (
            .in0(_gnd_net_),
            .in1(N__2176),
            .in2(_gnd_net_),
            .in3(N__2109),
            .lcout(\SPI.shift_regZ0Z_24 ),
            .ltout(),
            .carryin(_gnd_net_),
            .carryout(),
            .clk(\INVSPI.shift_reg_22C_net ),
            .ce(),
            .sr(_gnd_net_));
    defparam \SPI.shift_reg_25_LC_3_4_3 .C_ON=1'b0;
    defparam \SPI.shift_reg_25_LC_3_4_3 .SEQ_MODE=4'b1000;
    defparam \SPI.shift_reg_25_LC_3_4_3 .LUT_INIT=16'b1010101000000000;
    LogicCell40 \SPI.shift_reg_25_LC_3_4_3  (
            .in0(N__2181),
            .in1(_gnd_net_),
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
            .carryin(_gnd_net_),
            .carryout(),
            .clk(\INVSPI.shift_reg_71C_net ),
            .ce(),
            .sr(_gnd_net_));
    defparam \SPI.shift_reg_rst_rep1_rep1_LC_4_6_0 .C_ON=1'b0;
    defparam \SPI.shift_reg_rst_rep1_rep1_LC_4_6_0 .SEQ_MODE=4'b1010;
    defparam \SPI.shift_reg_rst_rep1_rep1_LC_4_6_0 .LUT_INIT=16'b1111111100000000;
    LogicCell40 \SPI.shift_reg_rst_rep1_rep1_LC_4_6_0  (
            .in0(_gnd_net_),
            .in1(_gnd_net_),
            .in2(_gnd_net_),
            .in3(N__3076),
            .lcout(\SPI.N_481_rep1_rep1 ),
            .ltout(),
            .carryin(_gnd_net_),
            .carryout(),
            .clk(\INVSPI.shift_reg_rst_rep1_rep1C_net ),
            .ce(),
            .sr(N__2925));
    defparam \SPI.shift_reg_rst_rep2_LC_4_6_1 .C_ON=1'b0;
    defparam \SPI.shift_reg_rst_rep2_LC_4_6_1 .SEQ_MODE=4'b1010;
    defparam \SPI.shift_reg_rst_rep2_LC_4_6_1 .LUT_INIT=16'b1010101010101010;
    LogicCell40 \SPI.shift_reg_rst_rep2_LC_4_6_1  (
            .in0(N__3077),
            .in1(_gnd_net_),
            .in2(_gnd_net_),
            .in3(_gnd_net_),
            .lcout(\SPI.N_481_rep2 ),
            .ltout(),
            .carryin(_gnd_net_),
            .carryout(),
            .clk(\INVSPI.shift_reg_rst_rep1_rep1C_net ),
            .ce(),
            .sr(N__2925));
    defparam \SPI.shift_reg_rst_rep2_fast_LC_4_6_2 .C_ON=1'b0;
    defparam \SPI.shift_reg_rst_rep2_fast_LC_4_6_2 .SEQ_MODE=4'b1010;
    defparam \SPI.shift_reg_rst_rep2_fast_LC_4_6_2 .LUT_INIT=16'b1111111100000000;
    LogicCell40 \SPI.shift_reg_rst_rep2_fast_LC_4_6_2  (
            .in0(_gnd_net_),
            .in1(_gnd_net_),
            .in2(_gnd_net_),
            .in3(N__3078),
            .lcout(\SPI.N_481_rep2_fast ),
            .ltout(),
            .carryin(_gnd_net_),
            .carryout(),
            .clk(\INVSPI.shift_reg_rst_rep1_rep1C_net ),
            .ce(),
            .sr(N__2925));
    defparam \SPI.shift_reg_rst_rep2_rep1_LC_4_6_3 .C_ON=1'b0;
    defparam \SPI.shift_reg_rst_rep2_rep1_LC_4_6_3 .SEQ_MODE=4'b1010;
    defparam \SPI.shift_reg_rst_rep2_rep1_LC_4_6_3 .LUT_INIT=16'b1010101010101010;
    LogicCell40 \SPI.shift_reg_rst_rep2_rep1_LC_4_6_3  (
            .in0(N__3079),
            .in1(_gnd_net_),
            .in2(_gnd_net_),
            .in3(_gnd_net_),
            .lcout(\SPI.N_481_rep2_rep1 ),
            .ltout(),
            .carryin(_gnd_net_),
            .carryout(),
            .clk(\INVSPI.shift_reg_rst_rep1_rep1C_net ),
            .ce(),
            .sr(N__2925));
    defparam \SPI.shift_reg_46_LC_4_7_0 .C_ON=1'b0;
    defparam \SPI.shift_reg_46_LC_4_7_0 .SEQ_MODE=4'b1000;
    defparam \SPI.shift_reg_46_LC_4_7_0 .LUT_INIT=16'b1010101000000000;
    LogicCell40 \SPI.shift_reg_46_LC_4_7_0  (
            .in0(N__2803),
            .in1(_gnd_net_),
            .in2(_gnd_net_),
            .in3(N__2769),
            .lcout(\SPI.shift_regZ0Z_46 ),
            .ltout(),
            .carryin(_gnd_net_),
            .carryout(),
            .clk(\INVSPI.shift_reg_46C_net ),
            .ce(),
            .sr(_gnd_net_));
    defparam \SPI.shift_reg_47_LC_4_7_1 .C_ON=1'b0;
    defparam \SPI.shift_reg_47_LC_4_7_1 .SEQ_MODE=4'b1000;
    defparam \SPI.shift_reg_47_LC_4_7_1 .LUT_INIT=16'b1100110000000000;
    LogicCell40 \SPI.shift_reg_47_LC_4_7_1  (
            .in0(_gnd_net_),
            .in1(N__2808),
            .in2(_gnd_net_),
            .in3(N__2853),
            .lcout(\SPI.shift_regZ0Z_47 ),
            .ltout(),
            .carryin(_gnd_net_),
            .carryout(),
            .clk(\INVSPI.shift_reg_46C_net ),
            .ce(),
            .sr(_gnd_net_));
    defparam \SPI.shift_reg_48_LC_4_7_2 .C_ON=1'b0;
    defparam \SPI.shift_reg_48_LC_4_7_2 .SEQ_MODE=4'b1000;
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
