Wireb/ICE40LP384_RPi_breakout/iCEcube2/PiDRO_Implmnt/sbt/outputs/simulation_netlist/PiDRO_sbt.vhd

-- ******************************************************************************

-- iCEcube Netlister

-- Version:            2020.12.27943

-- Build Date:         Dec  9 2020 18:18:06

-- File Generated:     May 3 2022 18:25:36

-- Purpose:            Post-Route Verilog/VHDL netlist for timing simulation

-- Copyright (C) 2006-2010 by Lattice Semiconductor Corp. All rights reserved.

-- ******************************************************************************

-- VHDL file for cell "PiDRO" view "INTERFACE"

library ieee;
use ieee.std_logic_1164.all;
use ieee.std_logic_arith.all;
use ieee.std_logic_unsigned.all;

library ice;
use ice.vcomponent_vital.all;

-- Entity of PiDRO
entity PiDRO is
port (
    Y_R : in std_logic;
    Y_B : in std_logic;
    B_R : in std_logic;
    B_B : in std_logic;
    Z_A : in std_logic;
    Y_A : in std_logic;
    X_R : in std_logic;
    X_B : in std_logic;
    SPI_SDI : in std_logic;
    Z_R : in std_logic;
    Z_B : in std_logic;
    SPI_SCK : in std_logic;
    A_R : in std_logic;
    A_B : in std_logic;
    SPI_SS : in std_logic;
    SPI_SDO : out std_logic;
    LED : out std_logic;
    B_A : in std_logic;
    A_A : in std_logic;
    X_A : in std_logic);
end PiDRO;

-- Architecture of PiDRO
-- View name is \INTERFACE\
architecture \INTERFACE\ of PiDRO is

signal \N__3253\ : std_logic;
signal \N__3252\ : std_logic;
signal \N__3251\ : std_logic;
signal \N__3244\ : std_logic;
signal \N__3243\ : std_logic;
signal \N__3242\ : std_logic;
signal \N__3235\ : std_logic;
signal \N__3234\ : std_logic;
signal \N__3233\ : std_logic;
signal \N__3226\ : std_logic;
signal \N__3225\ : std_logic;
signal \N__3224\ : std_logic;
signal \N__3217\ : std_logic;
signal \N__3216\ : std_logic;
signal \N__3215\ : std_logic;
signal \N__3198\ : std_logic;
signal \N__3195\ : std_logic;
signal \N__3192\ : std_logic;
signal \N__3189\ : std_logic;
signal \N__3186\ : std_logic;
signal \N__3183\ : std_logic;
signal \N__3180\ : std_logic;
signal \N__3177\ : std_logic;
signal \N__3174\ : std_logic;
signal \N__3171\ : std_logic;
signal \N__3168\ : std_logic;
signal \N__3165\ : std_logic;
signal \N__3162\ : std_logic;
signal \N__3161\ : std_logic;
signal \N__3160\ : std_logic;
signal \N__3159\ : std_logic;
signal \N__3158\ : std_logic;
signal \N__3157\ : std_logic;
signal \N__3156\ : std_logic;
signal \N__3155\ : std_logic;
signal \N__3154\ : std_logic;
signal \N__3153\ : std_logic;
signal \N__3138\ : std_logic;
signal \N__3131\ : std_logic;
signal \N__3126\ : std_logic;
signal \N__3123\ : std_logic;
signal \N__3120\ : std_logic;
signal \N__3117\ : std_logic;
signal \N__3114\ : std_logic;
signal \N__3111\ : std_logic;
signal \N__3110\ : std_logic;
signal \N__3109\ : std_logic;
signal \N__3108\ : std_logic;
signal \N__3107\ : std_logic;
signal \N__3106\ : std_logic;
signal \N__3105\ : std_logic;
signal \N__3102\ : std_logic;
signal \N__3089\ : std_logic;
signal \N__3088\ : std_logic;
signal \N__3083\ : std_logic;
signal \N__3080\ : std_logic;
signal \N__3079\ : std_logic;
signal \N__3078\ : std_logic;
signal \N__3077\ : std_logic;
signal \N__3076\ : std_logic;
signal \N__3073\ : std_logic;
signal \N__3070\ : std_logic;
signal \N__3061\ : std_logic;
signal \N__3054\ : std_logic;
signal \N__3051\ : std_logic;
signal \N__3048\ : std_logic;
signal \N__3045\ : std_logic;
signal \N__3042\ : std_logic;
signal \N__3039\ : std_logic;
signal \N__3036\ : std_logic;
signal \N__3033\ : std_logic;
signal \N__3030\ : std_logic;
signal \N__3027\ : std_logic;
signal \N__3024\ : std_logic;
signal \N__3023\ : std_logic;
signal \N__3022\ : std_logic;
signal \N__3021\ : std_logic;
signal \N__3020\ : std_logic;
signal \N__3019\ : std_logic;
signal \N__3018\ : std_logic;
signal \N__3017\ : std_logic;
signal \N__3016\ : std_logic;
signal \N__3015\ : std_logic;
signal \N__3010\ : std_logic;
signal \N__2997\ : std_logic;
signal \N__2992\ : std_logic;
signal \N__2985\ : std_logic;
signal \N__2984\ : std_logic;
signal \N__2983\ : std_logic;
signal \N__2982\ : std_logic;
signal \N__2981\ : std_logic;
signal \N__2980\ : std_logic;
signal \N__2979\ : std_logic;
signal \N__2978\ : std_logic;
signal \N__2977\ : std_logic;
signal \N__2976\ : std_logic;
signal \N__2973\ : std_logic;
signal \N__2970\ : std_logic;
signal \N__2965\ : std_logic;
signal \N__2952\ : std_logic;
signal \N__2949\ : std_logic;
signal \N__2940\ : std_logic;
signal \N__2937\ : std_logic;
signal \N__2934\ : std_logic;
signal \N__2931\ : std_logic;
signal \N__2928\ : std_logic;
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
signal \SPI.shift_regZ0Z_61\ : std_logic;
signal \SPI.shift_regZ0Z_68\ : std_logic;
signal \INVSPI.shift_reg_62C_net\ : std_logic;
signal \SPI.shift_regZ0Z_71\ : std_logic;
signal \SPI.N_481_rep1\ : std_logic;
signal \SPI.shift_regZ0Z_69\ : std_logic;
signal \SPI.shift_regZ0Z_70\ : std_logic;
signal \SPI.shift_regZ0Z_81\ : std_logic;
signal \SPI.shift_regZ0Z_82\ : std_logic;
signal \SPI.N_481_rep1_fast\ : std_logic;
signal \SPI.shift_regZ0Z_83\ : std_logic;
signal \SPI.shift_regZ0Z_84\ : std_logic;
signal \SPI.shift_regZ0Z_80\ : std_logic;
signal \INVSPI.shift_reg_71C_net\ : std_logic;
signal \SPI.N_481_rep2\ : std_logic;
signal \SPI.N_481_rep2_fast\ : std_logic;
signal \INVSPI.shift_reg_rst_rep1_rep1C_net\ : std_logic;
signal \SPI.shift_regZ0Z_46\ : std_logic;
signal \SPI.shift_regZ0Z_47\ : std_logic;
signal \SPI.shift_regZ0Z_48\ : std_logic;
signal \SPI.shift_regZ0Z_49\ : std_logic;
signal \SPI.shift_regZ0Z_50\ : std_logic;
signal \SPI.shift_regZ0Z_42\ : std_logic;
signal \SPI.shift_regZ0Z_43\ : std_logic;
signal \SPI.N_481_rep2_rep1\ : std_logic;
signal \SPI.shift_regZ0Z_44\ : std_logic;
signal \SPI.shift_regZ0Z_45\ : std_logic;
signal \INVSPI.shift_reg_46C_net\ : std_logic;
signal \SPI.shift_regZ0Z_99\ : std_logic;
signal \SPI.shift_regZ0Z_93\ : std_logic;
signal \SPI.shift_regZ0Z_98\ : std_logic;
signal \SPI.shift_regZ0Z_97\ : std_logic;
signal \SPI.shift_regZ0Z_96\ : std_logic;
signal \SPI.shift_regZ0Z_94\ : std_logic;
signal \SPI.shift_regZ0Z_95\ : std_logic;
signal \INVSPI.shift_reg_99C_net\ : std_logic;
signal \SPI.N_481_fast\ : std_logic;
signal \INVSPI.shift_reg_rst_fastC_net\ : std_logic;
signal \SPI.N_481_fast_fast\ : std_logic;
signal \SPI.shift_regZ0Z_119\ : std_logic;
signal \SPI_SDO_c\ : std_logic;
signal \INVSPI.SDOC_net\ : std_logic;
signal \LED_c\ : std_logic;
signal \SPI.LED_c_i\ : std_logic;
signal \SPI.shift_regZ0Z_72\ : std_logic;
signal \SPI.shift_regZ0Z_73\ : std_logic;
signal \SPI.shift_regZ0Z_74\ : std_logic;
signal \SPI.shift_regZ0Z_77\ : std_logic;
signal \SPI.shift_regZ0Z_75\ : std_logic;
signal \SPI.shift_regZ0Z_76\ : std_logic;
signal \SPI.N_481_rep1_rep1\ : std_logic;
signal \SPI.shift_regZ0Z_78\ : std_logic;
signal \SPI.shift_regZ0Z_79\ : std_logic;
signal \INVSPI.shift_reg_78C_net\ : std_logic;
signal \CONSTANT_ONE_NET\ : std_logic;
signal \_gnd_net_\ : std_logic;

signal \LED_wire\ : std_logic;
signal \SPI_SS_wire\ : std_logic;
signal \SPI_SDO_wire\ : std_logic;
signal \SPI_SDI_wire\ : std_logic;
signal \SPI_SCK_wire\ : std_logic;

begin
    LED <= \LED_wire\;
    \SPI_SS_wire\ <= SPI_SS;
    SPI_SDO <= \SPI_SDO_wire\;
    \SPI_SDI_wire\ <= SPI_SDI;
    \SPI_SCK_wire\ <= SPI_SCK;

    \LED_obuf_iopad\ : IO_PAD
    generic map (
            IO_STANDARD => "SB_LVCMOS",
            PULLUP => '0'
        )
    port map (
            OE => \N__3253\,
            DIN => \N__3252\,
            DOUT => \N__3251\,
            PACKAGEPIN => \LED_wire\
        );

    \LED_obuf_preio\ : PRE_IO
    generic map (
            NEG_TRIGGER => '0',
            PIN_TYPE => "011001"
        )
    port map (
            PADOEN => \N__3253\,
            PADOUT => \N__3252\,
            PADIN => \N__3251\,
            CLOCKENABLE => 'H',
            DOUT1 => '0',
            OUTPUTENABLE => '0',
            DIN0 => OPEN,
            DOUT0 => \N__2915\,
            INPUTCLK => '0',
            LATCHINPUTVALUE => '0',
            DIN1 => OPEN,
            OUTPUTCLK => '0'
        );

    \SPI_SS_ibuf_iopad\ : IO_PAD
    generic map (
            IO_STANDARD => "SB_LVCMOS",
            PULLUP => '0'
        )
    port map (
            OE => \N__3244\,
            DIN => \N__3243\,
            DOUT => \N__3242\,
            PACKAGEPIN => \SPI_SS_wire\
        );

    \SPI_SS_ibuf_preio\ : PRE_IO
    generic map (
            NEG_TRIGGER => '0',
            PIN_TYPE => "000001"
        )
    port map (
            PADOEN => \N__3244\,
            PADOUT => \N__3243\,
            PADIN => \N__3242\,
            CLOCKENABLE => 'H',
            DOUT1 => '0',
            OUTPUTENABLE => '0',
            DIN0 => \LED_c\,
            DOUT0 => '0',
            INPUTCLK => '0',
            LATCHINPUTVALUE => '0',
            DIN1 => OPEN,
            OUTPUTCLK => '0'
        );

    \SPI_SDO_obuf_iopad\ : IO_PAD
    generic map (
            IO_STANDARD => "SB_LVCMOS",
            PULLUP => '0'
        )
    port map (
            OE => \N__3235\,
            DIN => \N__3234\,
            DOUT => \N__3233\,
            PACKAGEPIN => \SPI_SDO_wire\
        );

    \SPI_SDO_obuf_preio\ : PRE_IO
    generic map (
            NEG_TRIGGER => '0',
            PIN_TYPE => "011001"
        )
    port map (
            PADOEN => \N__3235\,
            PADOUT => \N__3234\,
            PADIN => \N__3233\,
            CLOCKENABLE => 'H',
            DOUT1 => '0',
            OUTPUTENABLE => '0',
            DIN0 => OPEN,
            DOUT0 => \N__2934\,
            INPUTCLK => '0',
            LATCHINPUTVALUE => '0',
            DIN1 => OPEN,
            OUTPUTCLK => '0'
        );

    \SPI_SDI_ibuf_iopad\ : IO_PAD
    generic map (
            IO_STANDARD => "SB_LVCMOS",
            PULLUP => '0'
        )
    port map (
            OE => \N__3226\,
            DIN => \N__3225\,
            DOUT => \N__3224\,
            PACKAGEPIN => \SPI_SDI_wire\
        );

    \SPI_SDI_ibuf_preio\ : PRE_IO
    generic map (
            NEG_TRIGGER => '0',
            PIN_TYPE => "000001"
        )
    port map (
            PADOEN => \N__3226\,
            PADOUT => \N__3225\,
            PADIN => \N__3224\,
            CLOCKENABLE => 'H',
            DOUT1 => '0',
            OUTPUTENABLE => '0',
            DIN0 => \SPI_SDI_c\,
            DOUT0 => '0',
            INPUTCLK => '0',
            LATCHINPUTVALUE => '0',
            DIN1 => OPEN,
            OUTPUTCLK => '0'
        );

    \SPI_SCK_ibuf_gb_io_iopad\ : IO_PAD
    generic map (
            IO_STANDARD => "SB_LVCMOS",
            PULLUP => '0'
        )
    port map (
            OE => \N__3217\,
            DIN => \N__3216\,
            DOUT => \N__3215\,
            PACKAGEPIN => \SPI_SCK_wire\
        );

    \SPI_SCK_ibuf_gb_io_preio\ : PRE_IO
    generic map (
            NEG_TRIGGER => '0',
            PIN_TYPE => "000001"
        )
    port map (
            PADOEN => \N__3217\,
            PADOUT => \N__3216\,
            PADIN => \N__3215\,
            CLOCKENABLE => 'H',
            DOUT1 => '0',
            OUTPUTENABLE => '0',
            DIN0 => \SPI_SCK_ibuf_gb_io_gb_input\,
            DOUT0 => '0',
            INPUTCLK => '0',
            LATCHINPUTVALUE => '0',
            DIN1 => OPEN,
            OUTPUTCLK => '0'
        );

    \I__642\ : InMux
    port map (
            O => \N__3198\,
            I => \N__3195\
        );

    \I__641\ : LocalMux
    port map (
            O => \N__3195\,
            I => \SPI.shift_regZ0Z_72\
        );

    \I__640\ : InMux
    port map (
            O => \N__3192\,
            I => \N__3189\
        );

    \I__639\ : LocalMux
    port map (
            O => \N__3189\,
            I => \SPI.shift_regZ0Z_73\
        );

    \I__638\ : InMux
    port map (
            O => \N__3186\,
            I => \N__3183\
        );

    \I__637\ : LocalMux
    port map (
            O => \N__3183\,
            I => \SPI.shift_regZ0Z_74\
        );
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
            in3 => \N__2208\,
            lcout => \SPI.shift_regZ0Z_42\,
            ltout => OPEN,
            carryin => \_gnd_net_\,
            carryout => OPEN,
            clk => \INVSPI.shift_reg_38C_net\,
            ce => 'H',
            sr => \_gnd_net_\
        );

    \SPI.shift_reg_51_LC_3_7_5\ : LogicCell40
    generic map (
            C_ON => '0',
            SEQ_MODE => "1000",
            LUT_INIT => "1010101000000000"
        )
    port map (
            in0 => \N__2632\,
            in1 => \_gnd_net_\,
            in2 => \_gnd_net_\,
            in3 => \N__2829\,
            lcout => \SPI.shift_regZ0Z_51\,
            ltout => OPEN,
            carryin => \_gnd_net_\,
            carryout => OPEN,
            clk => \INVSPI.shift_reg_38C_net\,
            ce => 'H',
            sr => \_gnd_net_\
        );

    \SPI.shift_reg_52_LC_3_7_6\ : LogicCell40
    generic map (
            C_ON => '0',
            SEQ_MODE => "1000",
            LUT_INIT => "1100110000000000"
        )
    port map (
            in0 => \_gnd_net_\,
            in1 => \N__2631\,
            in2 => \_gnd_net_\,
            in3 => \N__2352\,
            lcout => \SPI.shift_regZ0Z_52\,
            ltout => OPEN,
            carryin => \_gnd_net_\,
            carryout => OPEN,
            clk => \INVSPI.shift_reg_38C_net\,
            ce => 'H',
            sr => \_gnd_net_\
        );
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
