Wireb/ICE40LP384_RPi_breakout/iCEcube2/PiDRO_Implmnt/sbt/outputs/simulation_netlist/spi_shifter_sbt.v

// ******************************************************************************

// iCEcube Netlister

// Version:            2020.12.27943

// Build Date:         Dec  9 2020 18:18:12

// File Generated:     Mar 1 2022 22:16:29

// Purpose:            Post-Route Verilog/VHDL netlist for timing simulation

// Copyright (C) 2006-2010 by Lattice Semiconductor Corp. All rights reserved.

// ******************************************************************************

// Verilog file for cell "spi_shifter" view "INTERFACE"

module spi_shifter (
    SPI_SS,
    SPI_SDO,
    SPI_SDI,
    LED,
    SPI_SCK);

    input SPI_SS;
    output SPI_SDO;
    input SPI_SDI;
    output LED;
    input SPI_SCK;

    wire N__2548;
    wire N__2547;
    wire N__2546;
    wire N__2539;
    wire N__2538;
    wire N__2537;
    wire N__2530;
    wire N__2529;
    wire N__2528;
    wire N__2521;
    wire N__2520;
    wire N__2519;
    wire N__2512;
    wire N__2511;
    wire N__2510;
    wire N__2493;
    wire N__2490;
    wire N__2487;
    wire N__2484;
    wire N__2481;
    wire N__2478;
    wire N__2475;
    wire N__2472;
    wire N__2469;
    wire N__2466;
    wire N__2463;
    wire N__2460;
    wire N__2457;
    wire N__2454;
    wire N__2451;
    wire N__2448;
    wire N__2445;
    wire N__2444;
    wire N__2443;
    wire N__2442;
    wire N__2441;
    wire N__2440;
    wire N__2439;
    wire N__2438;
    wire N__2437;
    wire N__2436;
    wire N__2435;
    wire N__2434;
    wire N__2433;
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
    wire shift_regZ0Z_14;
    wire shift_regZ0Z_15;
    wire shift_regZ0Z_16;
    wire shift_regZ0Z_17;
    wire INVshift_reg_10C_net;
    wire shift_regZ0Z_60;
    wire shift_regZ0Z_61;
    wire shift_regZ0Z_62;
    wire shift_regZ0Z_63;
    wire shift_regZ0Z_64;
    wire shift_regZ0Z_65;
    wire shift_regZ0Z_66;
    wire INVshift_reg_60C_net;
    wire shift_regZ0Z_51;
    wire shift_regZ0Z_52;
    wire shift_regZ0Z_53;
    wire shift_regZ0Z_54;
    wire shift_regZ0Z_55;
    wire shift_regZ0Z_56;
    wire shift_regZ0Z_57;
    wire shift_regZ0Z_58;
    wire shift_regZ0Z_59;
    wire INVshift_reg_52C_net;
    wire SPI_SDI_c;
    wire shift_regZ0Z_0;
    wire shift_regZ0Z_1;
    wire shift_regZ0Z_2;
    wire shift_regZ0Z_3;
    wire shift_regZ0Z_4;
    wire shift_regZ0Z_5;
    wire INVshift_reg_0C_net;
    wire shift_regZ0Z_90;
    wire shift_regZ0Z_84;
    wire shift_regZ0Z_85;
    wire shift_regZ0Z_86;
    wire shift_regZ0Z_87;
    wire shift_regZ0Z_88;
    wire shift_regZ0Z_89;
    wire INVshift_reg_90C_net;
    wire shift_regZ0Z_76;
    wire shift_regZ0Z_77;
    wire shift_regZ0Z_78;
    wire shift_regZ0Z_79;
    wire shift_regZ0Z_80;
    wire shift_regZ0Z_81;
    wire shift_regZ0Z_82;
    wire shift_regZ0Z_83;
    wire INVshift_reg_76C_net;
    wire shift_regZ0Z_67;
    wire shift_regZ0Z_68;
    wire shift_regZ0Z_69;
    wire shift_regZ0Z_70;
    wire shift_regZ0Z_71;
    wire shift_regZ0Z_72;
    wire shift_regZ0Z_73;
    wire shift_regZ0Z_74;
    wire shift_regZ0Z_75;
    wire INVshift_reg_68C_net;
    wire LED_c_i_g;
    wire LED_c;
    wire LED_c_i;
    wire _gnd_net_;

    IO_PAD SPI_SDO_obuf_iopad (
            .OE(N__2548),
            .DIN(N__2547),
            .DOUT(N__2546),
            .PACKAGEPIN(SPI_SDO));
    defparam SPI_SDO_obuf_preio.NEG_TRIGGER=1'b0;
    defparam SPI_SDO_obuf_preio.PIN_TYPE=6'b011001;
    PRE_IO SPI_SDO_obuf_preio (
            .PADOEN(N__2548),
            .PADOUT(N__2547),
            .PADIN(N__2546),
            .CLOCKENABLE(),
            .DOUT1(),
            .OUTPUTENABLE(),
            .DIN0(),
            .DOUT0(N__1692),
            .INPUTCLK(),
            .LATCHINPUTVALUE(),
            .DIN1(),
            .OUTPUTCLK());
    IO_PAD SPI_SDI_ibuf_iopad (
            .OE(N__2539),
            .DIN(N__2538),
            .DOUT(N__2537),
            .PACKAGEPIN(SPI_SDI));
    defparam SPI_SDI_ibuf_preio.NEG_TRIGGER=1'b0;
    defparam SPI_SDI_ibuf_preio.PIN_TYPE=6'b000001;
    PRE_IO SPI_SDI_ibuf_preio (
            .PADOEN(N__2539),
            .PADOUT(N__2538),
            .PADIN(N__2537),
            .CLOCKENABLE(),
            .DOUT1(),
            .OUTPUTENABLE(),
            .DIN0(SPI_SDI_c),
            .DOUT0(),
            .INPUTCLK(),
            .LATCHINPUTVALUE(),
            .DIN1(),
            .OUTPUTCLK());
    IO_PAD LED_obuf_iopad (
            .OE(N__2530),
            .DIN(N__2529),
            .DOUT(N__2528),
            .PACKAGEPIN(LED));
    defparam LED_obuf_preio.NEG_TRIGGER=1'b0;
    defparam LED_obuf_preio.PIN_TYPE=6'b011001;
    PRE_IO LED_obuf_preio (
            .PADOEN(N__2530),
            .PADOUT(N__2529),
            .PADIN(N__2528),
            .CLOCKENABLE(),
            .DOUT1(),
            .OUTPUTENABLE(),
            .DIN0(),
            .DOUT0(N__2388),
            .INPUTCLK(),
            .LATCHINPUTVALUE(),
            .DIN1(),
            .OUTPUTCLK());
    IO_PAD SPI_SS_ibuf_iopad (
            .OE(N__2521),
            .DIN(N__2520),
            .DOUT(N__2519),
            .PACKAGEPIN(SPI_SS));
    defparam SPI_SS_ibuf_preio.NEG_TRIGGER=1'b0;
    defparam SPI_SS_ibuf_preio.PIN_TYPE=6'b000001;
    PRE_IO SPI_SS_ibuf_preio (
            .PADOEN(N__2521),
            .PADOUT(N__2520),
            .PADIN(N__2519),
            .CLOCKENABLE(),
            .DOUT1(),
            .OUTPUTENABLE(),
            .DIN0(LED_c),
            .DOUT0(),
            .INPUTCLK(),
            .LATCHINPUTVALUE(),
            .DIN1(),
            .OUTPUTCLK());
    IO_PAD SPI_SCK_ibuf_gb_io_iopad (
            .OE(N__2512),
            .DIN(N__2511),
            .DOUT(N__2510),
            .PACKAGEPIN(SPI_SCK));
    defparam SPI_SCK_ibuf_gb_io_preio.NEG_TRIGGER=1'b0;
    defparam SPI_SCK_ibuf_gb_io_preio.PIN_TYPE=6'b000001;
    PRE_IO SPI_SCK_ibuf_gb_io_preio (
            .PADOEN(N__2512),
            .PADOUT(N__2511),
            .PADIN(N__2510),
            .CLOCKENABLE(),
            .DOUT1(),
            .OUTPUTENABLE(),
            .DIN0(SPI_SCK_ibuf_gb_io_gb_input),
            .DOUT0(),
            .INPUTCLK(),
            .LATCHINPUTVALUE(),
            .DIN1(),
            .OUTPUTCLK());
    InMux I__451 (
            .O(N__2493),
            .I(N__2490));
    LocalMux I__450 (
            .O(N__2490),
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
            .I(SPI_SCK_c_g));
    IoInMux I__153 (
            .O(N__1599),
            .I(N__1596));
    LocalMux I__152 (
            .O(N__1596),
            .I(N__1593));
    Span4Mux_s1_h I__151 (
            .O(N__1593),
            .I(N__1590));
    Span4Mux_h I__150 (
            .O(N__1590),
            .I(N__1587));
    Odrv4 I__149 (
            .O(N__1587),
            .I(SPI_SCK_ibuf_gb_io_gb_input));
    INV INVshift_reg_68C (
            .O(INVshift_reg_68C_net),
            .I(N__1655));
    INV INVshift_reg_76C (
            .O(INVshift_reg_76C_net),
            .I(N__1647));
    INV INVshift_reg_90C (
            .O(INVshift_reg_90C_net),
            .I(N__1654));
    INV INVshift_reg_0C (
            .O(INVshift_reg_0C_net),
            .I(N__1656));
    INV INVshift_reg_52C (
            .O(INVshift_reg_52C_net),
            .I(N__1653));
    INV INVshift_reg_60C (
            .O(INVshift_reg_60C_net),
            .I(N__1651));
    INV INVshift_reg_10C (
            .O(INVshift_reg_10C_net),
            .I(N__1644));
    INV INVshift_reg_9C (
            .O(INVshift_reg_9C_net),
            .I(N__1650));
    INV INVshift_reg_96C (
            .O(INVshift_reg_96C_net),
            .I(N__1652));
    INV INVshift_reg_44C (
            .O(INVshift_reg_44C_net),
            .I(N__1649));
    INV INVshift_reg_108C (
            .O(INVshift_reg_108C_net),
            .I(N__1641));
    INV INVshift_reg_114C (
            .O(INVshift_reg_114C_net),
            .I(N__1646));
    INV INVshift_reg_98C (
            .O(INVshift_reg_98C_net),
            .I(N__1648));
    INV INVshift_reg_36C (
            .O(INVshift_reg_36C_net),
            .I(N__1645));
    INV INVshift_reg_28C (
            .O(INVshift_reg_28C_net),
            .I(N__1643));
    INV INVshift_reg_20C (
            .O(INVshift_reg_20C_net),
            .I(N__1640));
    INV INVSPI_SDOZ0C (
            .O(INVSPI_SDOZ0C_net),
            .I(N__1642));
    ICE_GB SPI_SCK_ibuf_gb_io_gb (
            .USERSIGNALTOGLOBALBUFFER(N__1599),
            .GLOBALBUFFEROUTPUT(SPI_SCK_c_g));
    ICE_GB SPI_SS_ibuf_RNIMF4D_0 (
            .USERSIGNALTOGLOBALBUFFER(N__2370),
            .GLOBALBUFFEROUTPUT(LED_c_i_g));
    GND GND (
            .Y(GNDG0));
    VCC VCC (
            .Y(VCCG0));
    GND GND_Inst (
            .Y(_gnd_net_));
    defparam SPI_SDOZ0_LC_2_3_1.C_ON=1'b0;
    defparam SPI_SDOZ0_LC_2_3_1.SEQ_MODE=4'b1000;
    defparam SPI_SDOZ0_LC_2_3_1.LUT_INIT=16'b1111111100000000;
    LogicCell40 SPI_SDOZ0_LC_2_3_1 (
            .in0(_gnd_net_),
            .in1(_gnd_net_),
            .in2(_gnd_net_),
            .in3(N__1680),
            .lcout(SPI_SDO_c),
            .ltout(),
            .carryin(_gnd_net_),
            .carryout(),
            .clk(INVSPI_SDOZ0C_net),
            .ce(N__2433),
            .sr(_gnd_net_));
    defparam shift_reg_119_LC_2_3_2.C_ON=1'b0;
    defparam shift_reg_119_LC_2_3_2.SEQ_MODE=4'b1000;
    defparam shift_reg_119_LC_2_3_2.LUT_INIT=16'b1111111100000000;
    LogicCell40 shift_reg_119_LC_2_3_2 (
            .in0(_gnd_net_),
            .in1(_gnd_net_),
            .in2(_gnd_net_),
            .in3(N__1674),
            .lcout(shift_regZ0Z_119),
            .ltout(),
            .carryin(_gnd_net_),
            .carryout(),
            .clk(INVSPI_SDOZ0C_net),
            .ce(N__2433),
            .sr(_gnd_net_));
    defparam shift_reg_118_LC_2_3_3.C_ON=1'b0;
    defparam shift_reg_118_LC_2_3_3.SEQ_MODE=4'b1000;
    defparam shift_reg_118_LC_2_3_3.LUT_INIT=16'b1111111100000000;
    LogicCell40 shift_reg_118_LC_2_3_3 (
            .in0(_gnd_net_),
            .in1(_gnd_net_),
            .in2(_gnd_net_),
            .in3(N__1668),
            .lcout(shift_regZ0Z_118),
            .ltout(),
            .carryin(_gnd_net_),
            .carryout(),
            .clk(INVSPI_SDOZ0C_net),
            .ce(N__2433),
            .sr(_gnd_net_));
    defparam shift_reg_117_LC_2_3_4.C_ON=1'b0;
    defparam shift_reg_117_LC_2_3_4.SEQ_MODE=4'b1000;
    defparam shift_reg_117_LC_2_3_4.LUT_INIT=16'b1111111100000000;
    LogicCell40 shift_reg_117_LC_2_3_4 (
            .in0(_gnd_net_),
            .in1(_gnd_net_),
            .in2(_gnd_net_),
            .in3(N__1662),
            .lcout(shift_regZ0Z_117),
            .ltout(),
            .carryin(_gnd_net_),
            .carryout(),
            .clk(INVSPI_SDOZ0C_net),
            .ce(N__2433),
            .sr(_gnd_net_));
    defparam shift_reg_116_LC_2_3_5.C_ON=1'b0;
    defparam shift_reg_116_LC_2_3_5.SEQ_MODE=4'b1000;
    defparam shift_reg_116_LC_2_3_5.LUT_INIT=16'b1111111100000000;
    LogicCell40 shift_reg_116_LC_2_3_5 (
            .in0(_gnd_net_),
            .in1(_gnd_net_),
            .in2(_gnd_net_),
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
    defparam shift_reg_74_LC_5_5_6.C_ON=1'b0;
    defparam shift_reg_74_LC_5_5_6.SEQ_MODE=4'b1000;
    defparam shift_reg_74_LC_5_5_6.LUT_INIT=16'b1111111100000000;
    LogicCell40 shift_reg_74_LC_5_5_6 (
            .in0(_gnd_net_),
            .in1(_gnd_net_),
            .in2(_gnd_net_),
            .in3(N__2463),
            .lcout(shift_regZ0Z_74),
            .ltout(),
            .carryin(_gnd_net_),
            .carryout(),
            .clk(INVshift_reg_68C_net),
            .ce(N__2436),
            .sr(_gnd_net_));
    defparam shift_reg_75_LC_5_5_7.C_ON=1'b0;
    defparam shift_reg_75_LC_5_5_7.SEQ_MODE=4'b1000;
    defparam shift_reg_75_LC_5_5_7.LUT_INIT=16'b1111111100000000;
    LogicCell40 shift_reg_75_LC_5_5_7 (
            .in0(_gnd_net_),
            .in1(_gnd_net_),
            .in2(_gnd_net_),
            .in3(N__2457),
            .lcout(shift_regZ0Z_75),
            .ltout(),
            .carryin(_gnd_net_),
            .carryout(),
            .clk(INVshift_reg_68C_net),
            .ce(N__2436),
            .sr(_gnd_net_));
    defparam SPI_SS_ibuf_RNIMF4D_LC_6_4_4.C_ON=1'b0;
    defparam SPI_SS_ibuf_RNIMF4D_LC_6_4_4.SEQ_MODE=4'b0000;
    defparam SPI_SS_ibuf_RNIMF4D_LC_6_4_4.LUT_INIT=16'b0011001100110011;
    LogicCell40 SPI_SS_ibuf_RNIMF4D_LC_6_4_4 (
            .in0(_gnd_net_),
            .in1(N__2387),
            .in2(_gnd_net_),
            .in3(_gnd_net_),
            .lcout(LED_c_i),
            .ltout(),
            .carryin(_gnd_net_),
            .carryout(),
            .clk(_gnd_net_),
            .ce(),
            .sr(_gnd_net_));
endmodule // spi_shifter
