Wireb/ICE40LP384_RPi_breakout/iCEcube2/PiDRO_Implmnt/sbt/outputs/simulation_netlist/spi_shifter_sbt.vhd

-- ******************************************************************************

-- iCEcube Netlister

-- Version:            2020.12.27943

-- Build Date:         Dec  9 2020 18:18:06

-- File Generated:     Mar 1 2022 22:16:29

-- Purpose:            Post-Route Verilog/VHDL netlist for timing simulation

-- Copyright (C) 2006-2010 by Lattice Semiconductor Corp. All rights reserved.

-- ******************************************************************************

-- VHDL file for cell "spi_shifter" view "INTERFACE"

library ieee;
use ieee.std_logic_1164.all;
use ieee.std_logic_arith.all;
use ieee.std_logic_unsigned.all;

library ice;
use ice.vcomponent_vital.all;

-- Entity of spi_shifter
entity spi_shifter is
port (
    SPI_SS : in std_logic;
    SPI_SDO : out std_logic;
    SPI_SDI : in std_logic;
    LED : out std_logic;
    SPI_SCK : in std_logic);
end spi_shifter;

-- Architecture of spi_shifter
-- View name is \INTERFACE\
architecture \INTERFACE\ of spi_shifter is

signal \N__2548\ : std_logic;
signal \N__2547\ : std_logic;
signal \N__2546\ : std_logic;
signal \N__2539\ : std_logic;
signal \N__2538\ : std_logic;
signal \N__2537\ : std_logic;
signal \N__2530\ : std_logic;
signal \N__2529\ : std_logic;
signal \N__2528\ : std_logic;
signal \N__2521\ : std_logic;
signal \N__2520\ : std_logic;
signal \N__2519\ : std_logic;
signal \N__2512\ : std_logic;
signal \N__2511\ : std_logic;
signal \N__2510\ : std_logic;
signal \N__2493\ : std_logic;
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
signal \shift_regZ0Z_59\ : std_logic;
signal \INVshift_reg_52C_net\ : std_logic;
signal \SPI_SDI_c\ : std_logic;
signal \shift_regZ0Z_0\ : std_logic;
signal \shift_regZ0Z_1\ : std_logic;
signal \shift_regZ0Z_2\ : std_logic;
signal \shift_regZ0Z_3\ : std_logic;
signal \shift_regZ0Z_4\ : std_logic;
signal \shift_regZ0Z_5\ : std_logic;
signal \INVshift_reg_0C_net\ : std_logic;
signal \shift_regZ0Z_90\ : std_logic;
signal \shift_regZ0Z_84\ : std_logic;
signal \shift_regZ0Z_85\ : std_logic;
signal \shift_regZ0Z_86\ : std_logic;
signal \shift_regZ0Z_87\ : std_logic;
signal \shift_regZ0Z_88\ : std_logic;
signal \shift_regZ0Z_89\ : std_logic;
signal \INVshift_reg_90C_net\ : std_logic;
signal \shift_regZ0Z_76\ : std_logic;
signal \shift_regZ0Z_77\ : std_logic;
signal \shift_regZ0Z_78\ : std_logic;
signal \shift_regZ0Z_79\ : std_logic;
signal \shift_regZ0Z_80\ : std_logic;
signal \shift_regZ0Z_81\ : std_logic;
signal \shift_regZ0Z_82\ : std_logic;
signal \shift_regZ0Z_83\ : std_logic;
signal \INVshift_reg_76C_net\ : std_logic;
signal \shift_regZ0Z_67\ : std_logic;
signal \shift_regZ0Z_68\ : std_logic;
signal \shift_regZ0Z_69\ : std_logic;
signal \shift_regZ0Z_70\ : std_logic;
signal \shift_regZ0Z_71\ : std_logic;
signal \shift_regZ0Z_72\ : std_logic;
signal \shift_regZ0Z_73\ : std_logic;
signal \shift_regZ0Z_74\ : std_logic;
signal \shift_regZ0Z_75\ : std_logic;
signal \INVshift_reg_68C_net\ : std_logic;
signal \LED_c_i_g\ : std_logic;
signal \LED_c\ : std_logic;
signal \LED_c_i\ : std_logic;
signal \_gnd_net_\ : std_logic;

signal \SPI_SDO_wire\ : std_logic;
signal \SPI_SDI_wire\ : std_logic;
signal \LED_wire\ : std_logic;
signal \SPI_SS_wire\ : std_logic;
signal \SPI_SCK_wire\ : std_logic;

begin
    SPI_SDO <= \SPI_SDO_wire\;
    \SPI_SDI_wire\ <= SPI_SDI;
    LED <= \LED_wire\;
    \SPI_SS_wire\ <= SPI_SS;
    \SPI_SCK_wire\ <= SPI_SCK;

    \SPI_SDO_obuf_iopad\ : IO_PAD
    generic map (
            IO_STANDARD => "SB_LVCMOS",
            PULLUP => '0'
        )
    port map (
            OE => \N__2548\,
            DIN => \N__2547\,
            DOUT => \N__2546\,
            PACKAGEPIN => \SPI_SDO_wire\
        );

    \SPI_SDO_obuf_preio\ : PRE_IO
    generic map (
            NEG_TRIGGER => '0',
            PIN_TYPE => "011001"
        )
    port map (
            PADOEN => \N__2548\,
            PADOUT => \N__2547\,
            PADIN => \N__2546\,
            CLOCKENABLE => 'H',
            DOUT1 => '0',
            OUTPUTENABLE => '0',
            DIN0 => OPEN,
            DOUT0 => \N__1692\,
            INPUTCLK => '0',
            LATCHINPUTVALUE => '0',
            DIN1 => OPEN,
            OUTPUTCLK => '0'
        );

    \SPI_SDI_ibuf_iopad\ : IO_PAD
    generic map (
            IO_STANDARD => "SB_LVCMOS",
            PULLUP => '0'
        )
    port map (
            OE => \N__2539\,
            DIN => \N__2538\,
            DOUT => \N__2537\,
            PACKAGEPIN => \SPI_SDI_wire\
        );

    \SPI_SDI_ibuf_preio\ : PRE_IO
    generic map (
            NEG_TRIGGER => '0',
            PIN_TYPE => "000001"
        )
    port map (
            PADOEN => \N__2539\,
            PADOUT => \N__2538\,
            PADIN => \N__2537\,
            CLOCKENABLE => 'H',
            DOUT1 => '0',
            OUTPUTENABLE => '0',
            DIN0 => \SPI_SDI_c\,
            DOUT0 => '0',
            INPUTCLK => '0',
            LATCHINPUTVALUE => '0',
            DIN1 => OPEN,
            OUTPUTCLK => '0'
        );

    \LED_obuf_iopad\ : IO_PAD
    generic map (
            IO_STANDARD => "SB_LVCMOS",
            PULLUP => '0'
        )
    port map (
            OE => \N__2530\,
            DIN => \N__2529\,
            DOUT => \N__2528\,
            PACKAGEPIN => \LED_wire\
        );

    \LED_obuf_preio\ : PRE_IO
    generic map (
            NEG_TRIGGER => '0',
            PIN_TYPE => "011001"
        )
    port map (
            PADOEN => \N__2530\,
            PADOUT => \N__2529\,
            PADIN => \N__2528\,
            CLOCKENABLE => 'H',
            DOUT1 => '0',
            OUTPUTENABLE => '0',
            DIN0 => OPEN,
            DOUT0 => \N__2388\,
            INPUTCLK => '0',
            LATCHINPUTVALUE => '0',
            DIN1 => OPEN,
            OUTPUTCLK => '0'
        );

    \SPI_SS_ibuf_iopad\ : IO_PAD
    generic map (
            IO_STANDARD => "SB_LVCMOS",
            PULLUP => '0'
        )
    port map (
            OE => \N__2521\,
            DIN => \N__2520\,
            DOUT => \N__2519\,
            PACKAGEPIN => \SPI_SS_wire\
        );

    \SPI_SS_ibuf_preio\ : PRE_IO
    generic map (
            NEG_TRIGGER => '0',
            PIN_TYPE => "000001"
        )
    port map (
            PADOEN => \N__2521\,
            PADOUT => \N__2520\,
            PADIN => \N__2519\,
            CLOCKENABLE => 'H',
            DOUT1 => '0',
            OUTPUTENABLE => '0',
            DIN0 => \LED_c\,
            DOUT0 => '0',
            INPUTCLK => '0',
            LATCHINPUTVALUE => '0',
            DIN1 => OPEN,
            OUTPUTCLK => '0'
        );

    \SPI_SCK_ibuf_gb_io_iopad\ : IO_PAD
    generic map (
            IO_STANDARD => "SB_LVCMOS",
            PULLUP => '0'
        )
    port map (
            OE => \N__2512\,
            DIN => \N__2511\,
            DOUT => \N__2510\,
            PACKAGEPIN => \SPI_SCK_wire\
        );

    \SPI_SCK_ibuf_gb_io_preio\ : PRE_IO
    generic map (
            NEG_TRIGGER => '0',
            PIN_TYPE => "000001"
        )
    port map (
            PADOEN => \N__2512\,
            PADOUT => \N__2511\,
            PADIN => \N__2510\,
            CLOCKENABLE => 'H',
            DOUT1 => '0',
            OUTPUTENABLE => '0',
            DIN0 => \SPI_SCK_ibuf_gb_io_gb_input\,
            DOUT0 => '0',
            INPUTCLK => '0',
            LATCHINPUTVALUE => '0',
            DIN1 => OPEN,
            OUTPUTCLK => '0'
        );

    \I__451\ : InMux
    port map (
            O => \N__2493\,
            I => \N__2490\
        );

    \I__450\ : LocalMux
    port map (
            O => \N__2490\,
            I => \shift_regZ0Z_68\
        );

    \I__449\ : InMux
    port map (
            O => \N__2487\,
            I => \N__2484\
        );

    \I__448\ : LocalMux
    port map (
            O => \N__2484\,
            I => \shift_regZ0Z_69\
        );

    \I__447\ : InMux
    port map (
            O => \N__2481\,
            I => \N__2478\
        );

    \I__446\ : LocalMux
    port map (
            O => \N__2478\,
            I => \shift_regZ0Z_70\
        );

    \I__445\ : InMux
    port map (
            O => \N__2475\,
            I => \N__2472\
        );

    \I__444\ : LocalMux
    port map (
            O => \N__2472\,
            I => \shift_regZ0Z_71\
        );

    \I__443\ : InMux
    port map (
            O => \N__2469\,
            I => \N__2466\
        );

    \I__442\ : LocalMux
    port map (
            O => \N__2466\,
            I => \shift_regZ0Z_72\
        );

    \I__441\ : InMux
    port map (
            O => \N__2463\,
            I => \N__2460\
        );

    \I__440\ : LocalMux
    port map (
            O => \N__2460\,
            I => \shift_regZ0Z_73\
        );

    \I__439\ : InMux
    port map (
            O => \N__2457\,
            I => \N__2454\
        );

    \I__438\ : LocalMux
    port map (
            O => \N__2454\,
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
            O => \N__2253\,
            I => \shift_regZ0Z_87\
        );

    \I__370\ : InMux
    port map (
            O => \N__2250\,
            I => \N__2247\
        );

    \I__369\ : LocalMux
    port map (
            O => \N__2247\,
            I => \shift_regZ0Z_88\
        );

    \I__368\ : InMux
    port map (
            O => \N__2244\,
            I => \N__2241\
        );

    \I__367\ : LocalMux
    port map (
            O => \N__2241\,
            I => \shift_regZ0Z_89\
        );

    \I__366\ : InMux
    port map (
            O => \N__2238\,
            I => \N__2235\
        );

    \I__365\ : LocalMux
    port map (
            O => \N__2235\,
            I => \shift_regZ0Z_54\
        );

    \I__364\ : InMux
    port map (
            O => \N__2232\,
            I => \N__2229\
        );

    \I__363\ : LocalMux
    port map (
            O => \N__2229\,
            I => \shift_regZ0Z_55\
        );

    \I__362\ : InMux
    port map (
            O => \N__2226\,
            I => \N__2223\
        );

    \I__361\ : LocalMux
    port map (
            O => \N__2223\,
            I => \shift_regZ0Z_56\
        );
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
